Xenii1642/Xii-Boy-Ultra/Images/Main-Menu.jpg

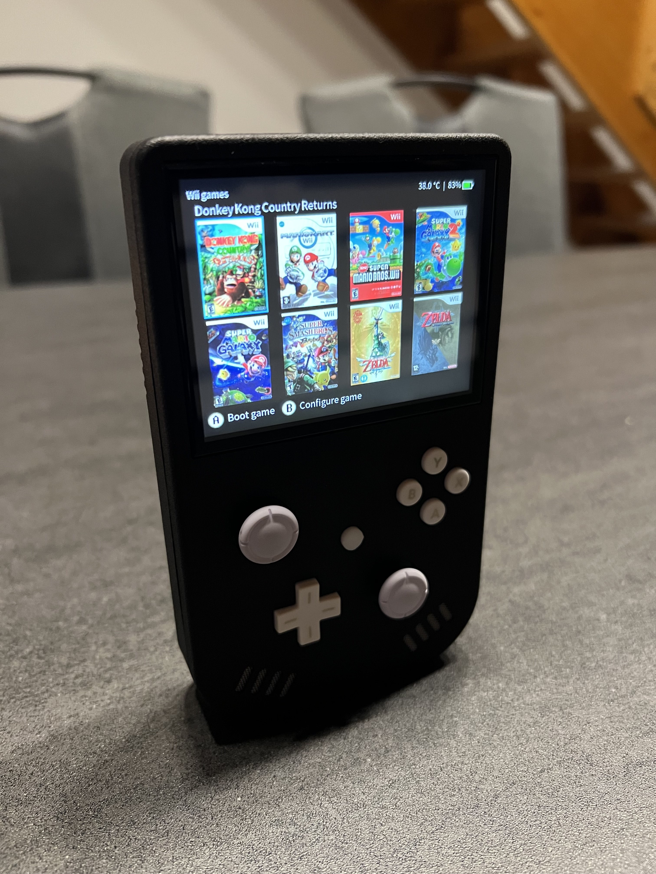
Images/Main-Menu.jpg
